Schievel1/baby_got_track/images/diodes-in.jpg

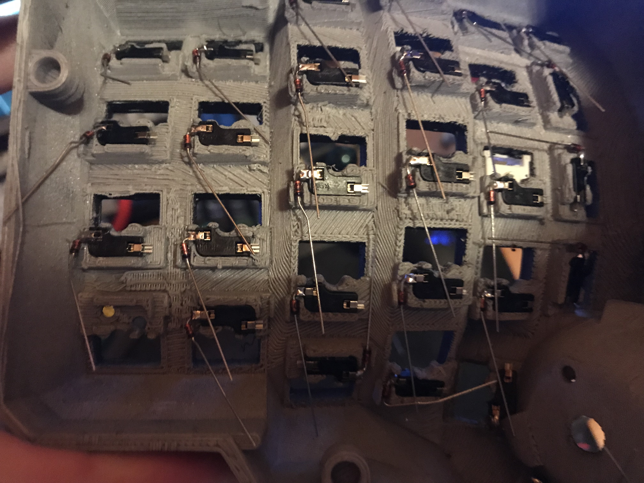
images/diodes-in.jpg
