Schievel1/baby_got_track/images/horizontal-lines.jpg

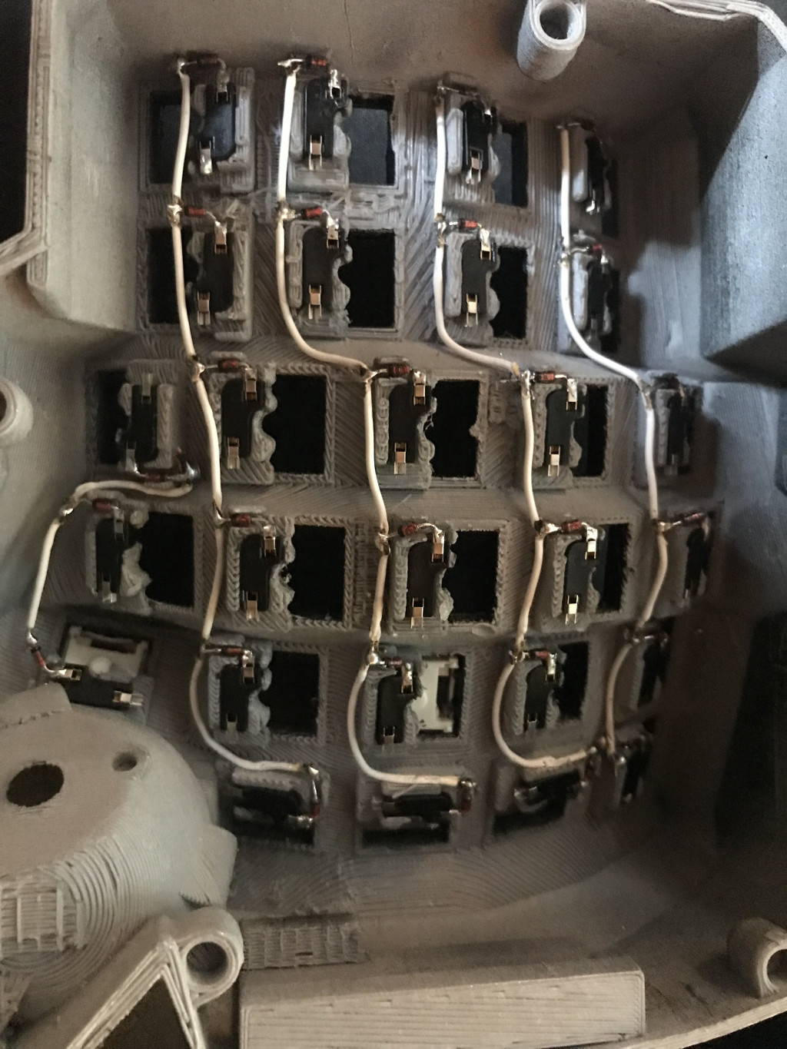
images/horizontal-lines.jpg
