Schievel1/baby_got_track/images/hot_glue_swaps.jpg

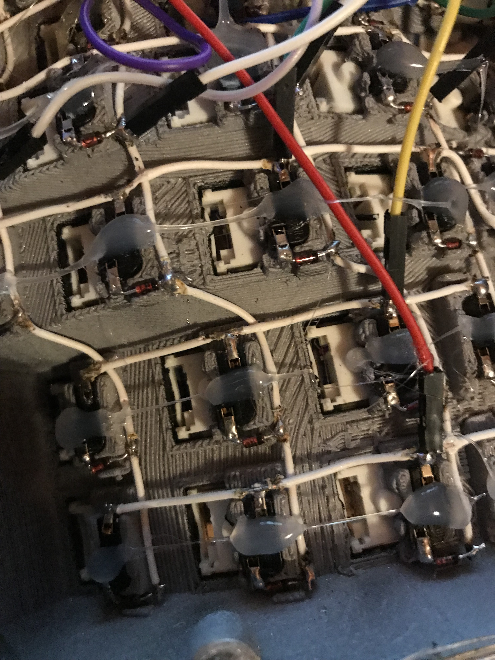
images/hot_glue_swaps.jpg
