Schievel1/baby_got_track/images/jumpers_to_arduino.jpg

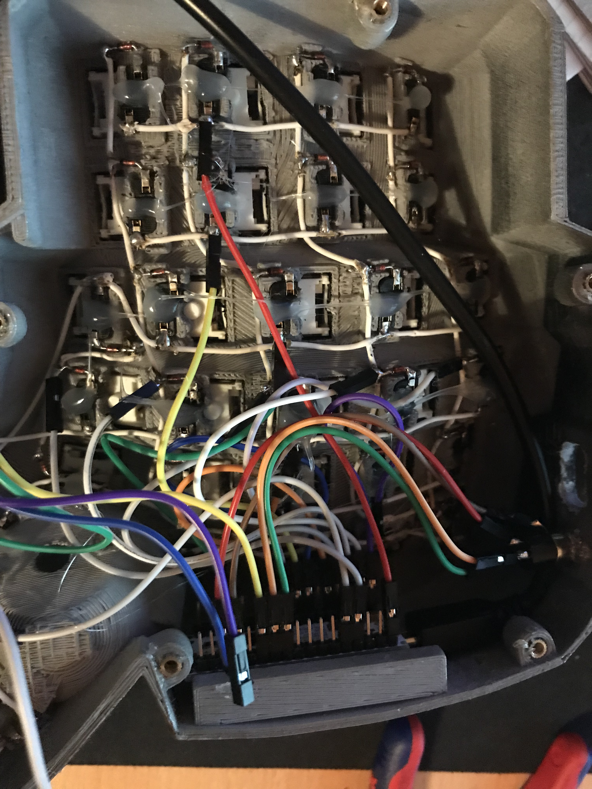
images/jumpers_to_arduino.jpg
