Schievel1/baby_got_track/images/jumpers_to_mat.jpg

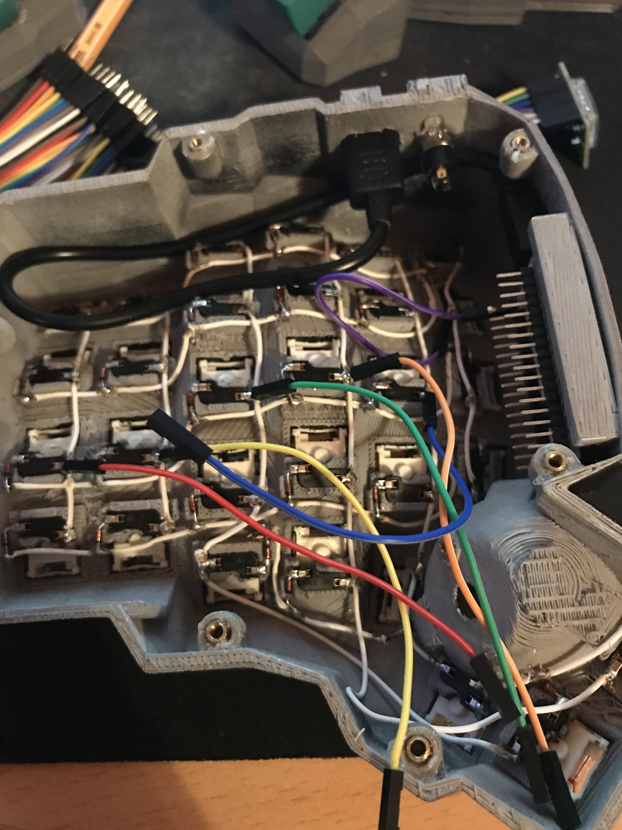
images/jumpers_to_mat.jpg
