Schievel1/baby_got_track/images/layer0.jpg

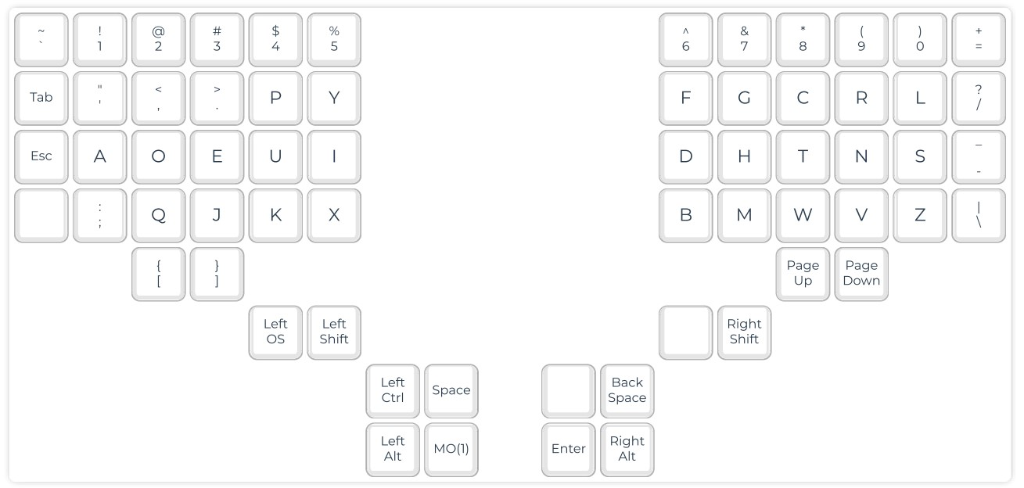
images/layer0.jpg
