Schievel1/baby_got_track/images/layer1.jpg

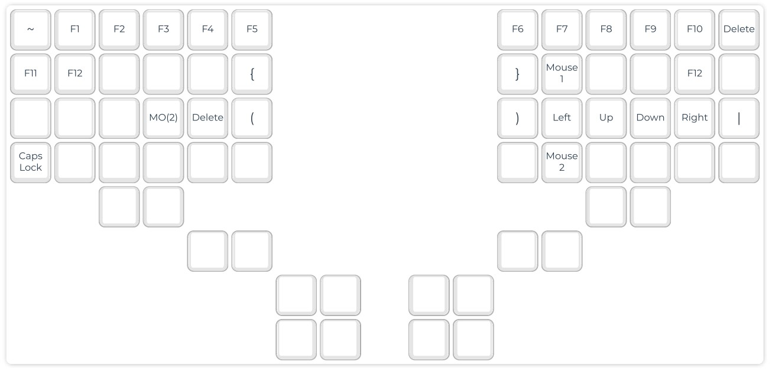
images/layer1.jpg
