Schievel1/baby_got_track/images/more_images/IMG_9945.jpg

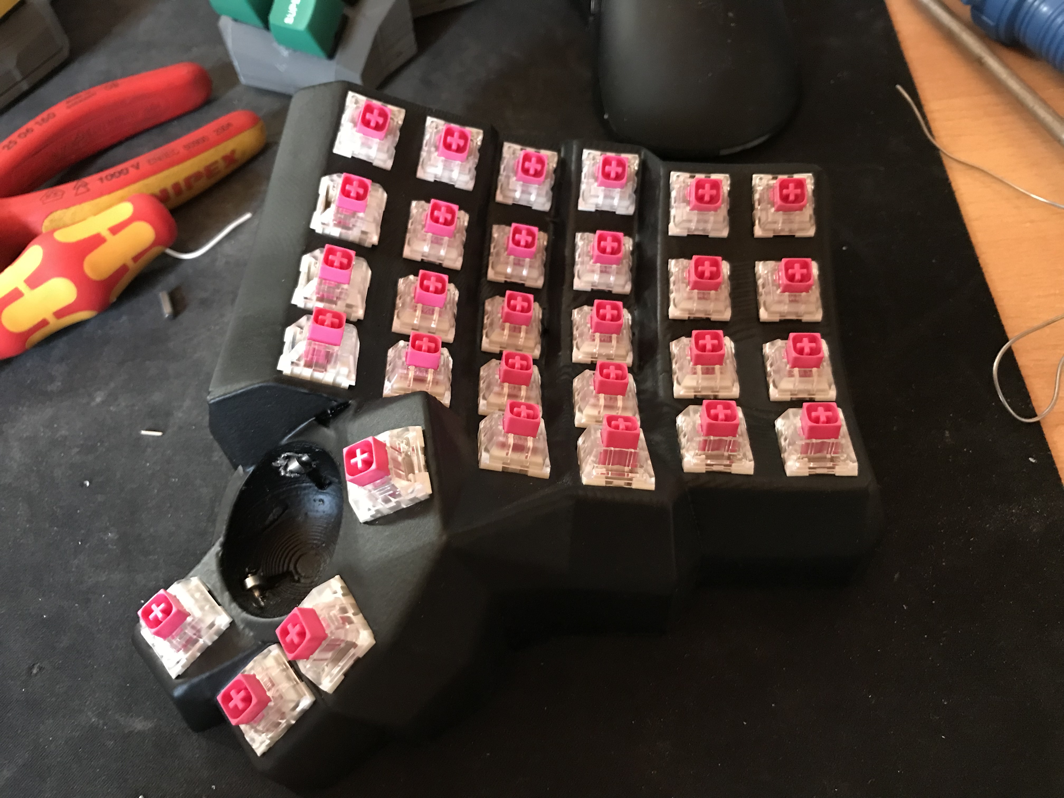
images/more_images/IMG_9945.jpg
