Schievel1/baby_got_track/images/more_images/Pinout-Micro_latest.png

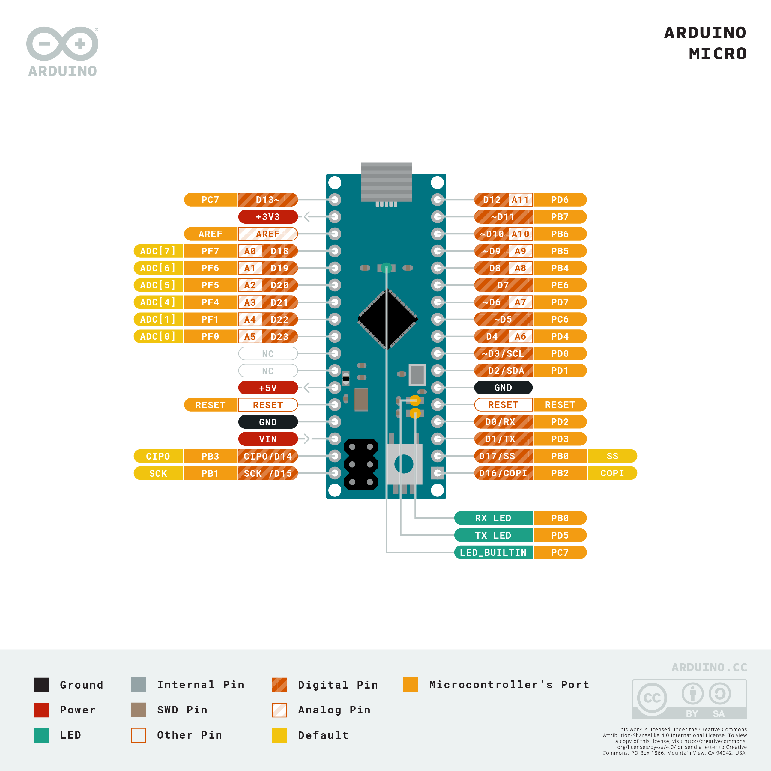
images/more_images/Pinout-Micro_latest.png
