Schievel1/baby_got_track/images/reset_connect.jpg

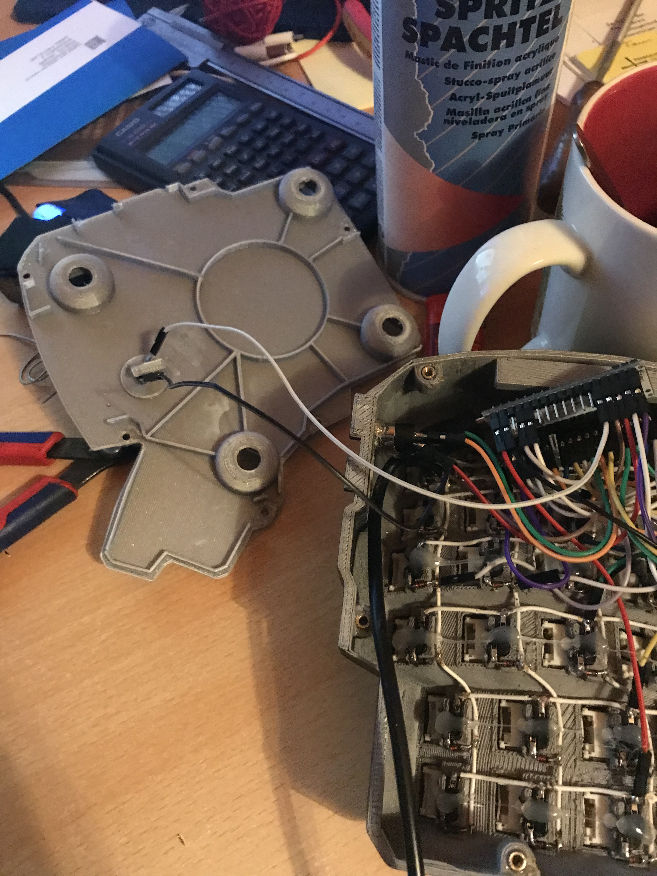
images/reset_connect.jpg
