Schievel1/baby_got_track/images/reset_switch_in.jpg

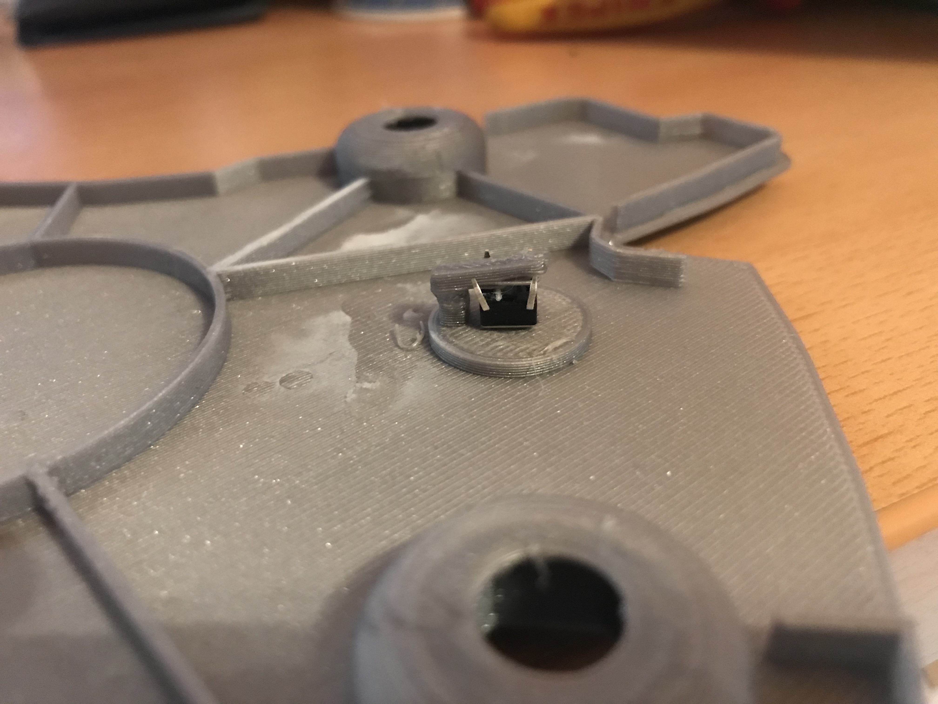
images/reset_switch_in.jpg
