Schievel1/baby_got_track/images/wokk.jpg

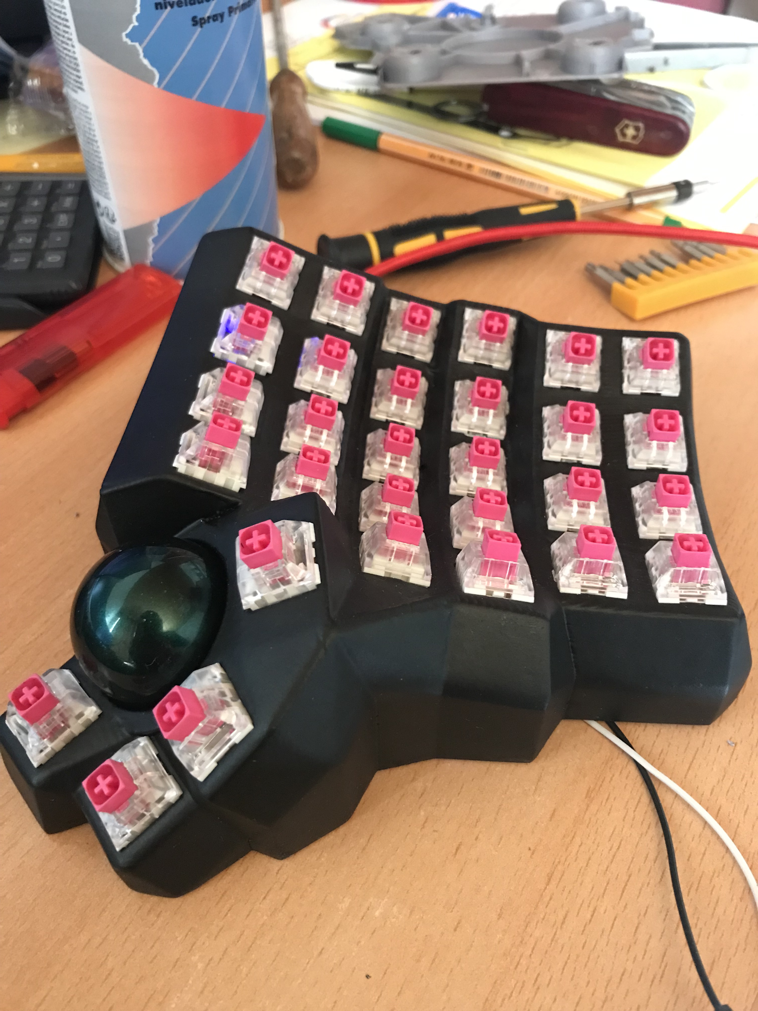
images/wokk.jpg
