Schievel1/baby_got_track/images/solder_reset.jpg

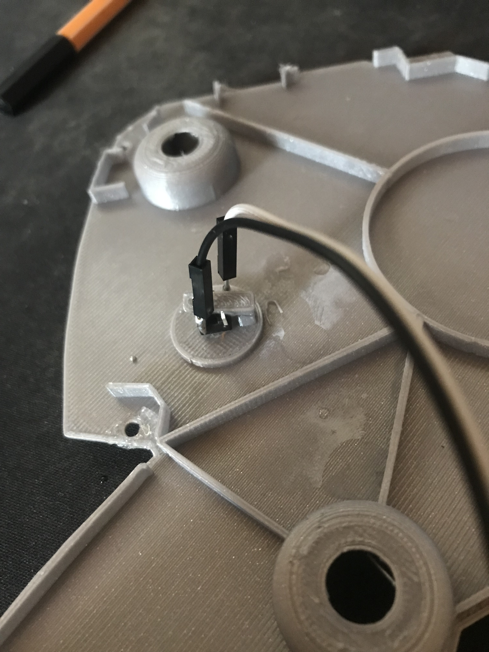
images/solder_reset.jpg
